xddcore/PineconePiWatch/Report&requirement/dev_img/%N)9%Y6C()[AU40SE[%3J6S.png

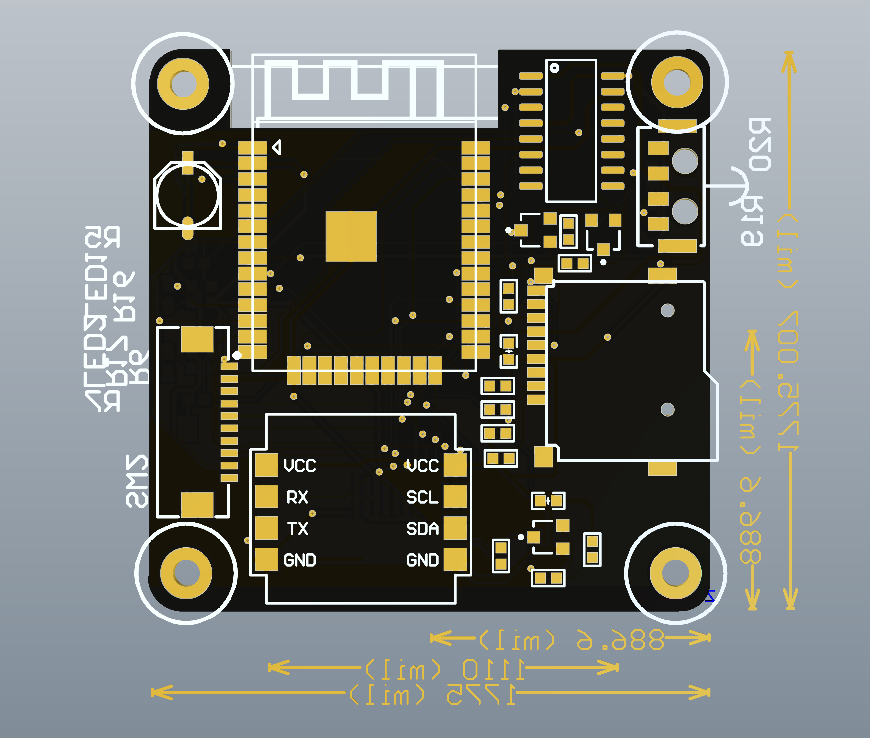
Report&requirement/dev_img/%N)9%Y6C()[AU40SE[%3J6S.png
