xddcore/PineconePiWatch/Report&requirement/dev_img/Django启动.png

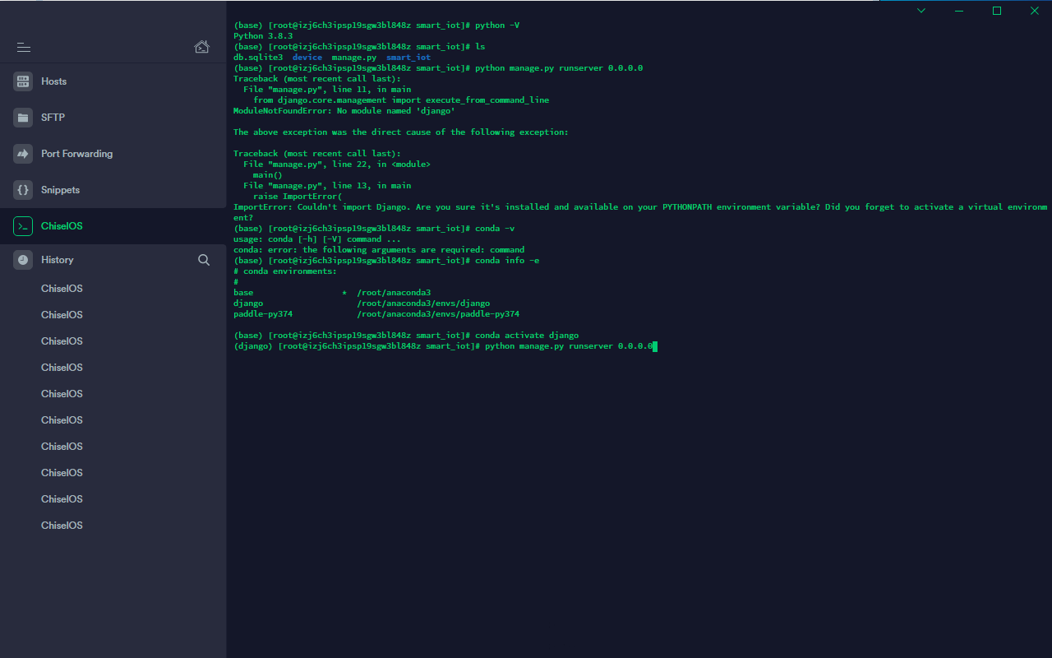
Report&requirement/dev_img/Django启动.png
