xddcore/PineconePiWatch/Report&requirement/dev_img/DRC无错误.png

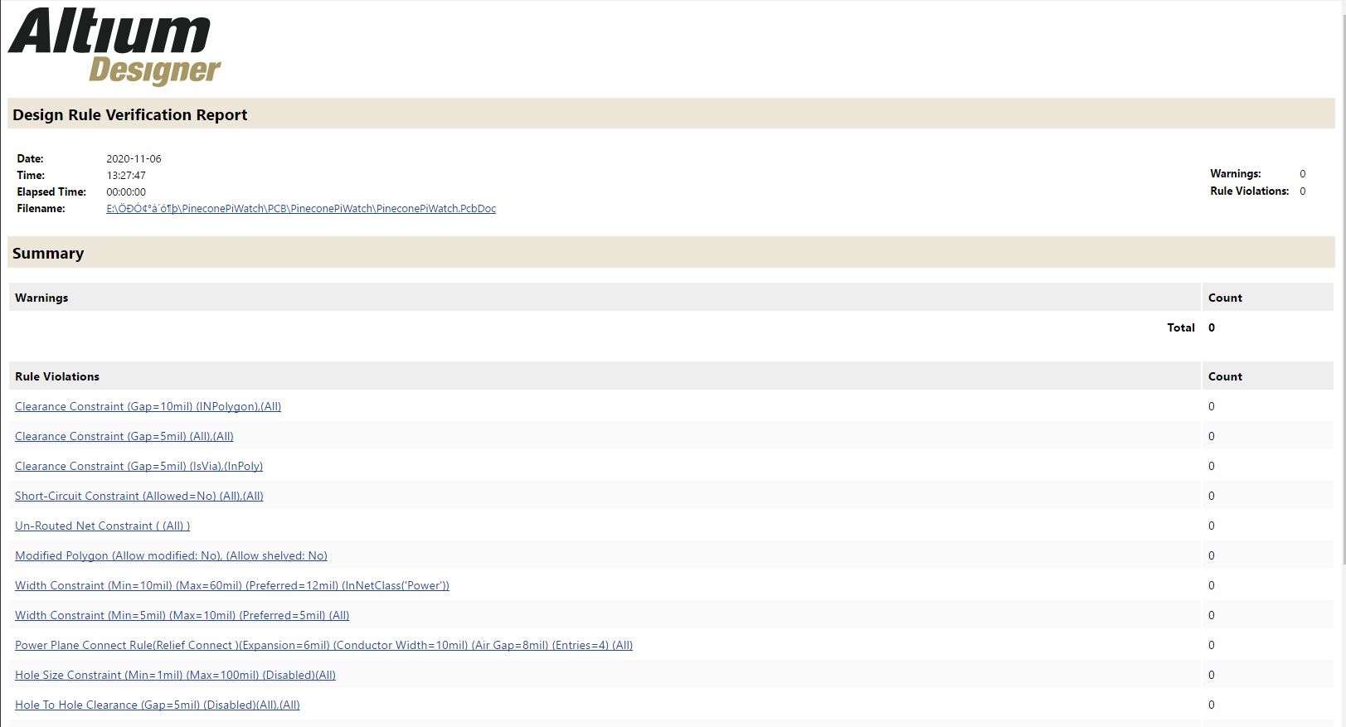
Report&requirement/dev_img/DRC无错误.png
