xddcore/PineconePiWatch/Report&requirement/dev_img/low power control/d21b8d4ec1d9de5b9760d6d338e170ff.png

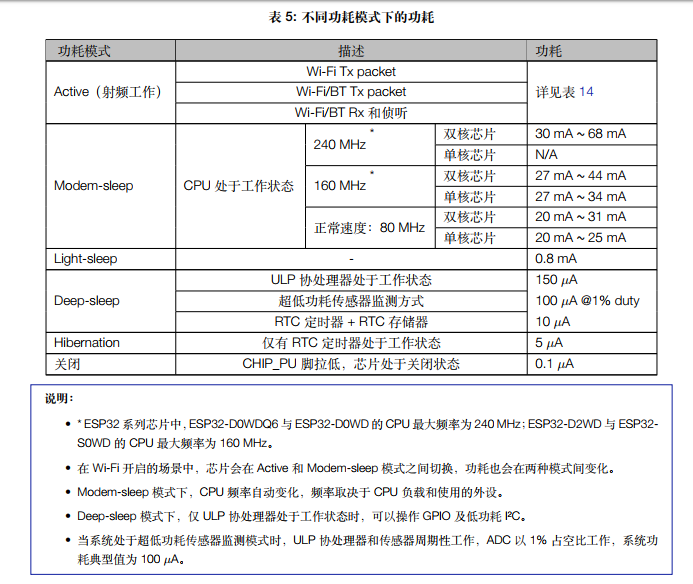
Report&requirement/dev_img/low power control/d21b8d4ec1d9de5b9760d6d338e170ff.png
