xddcore/PineconePiWatch/Report&requirement/dev_img/low power control/tft1.png

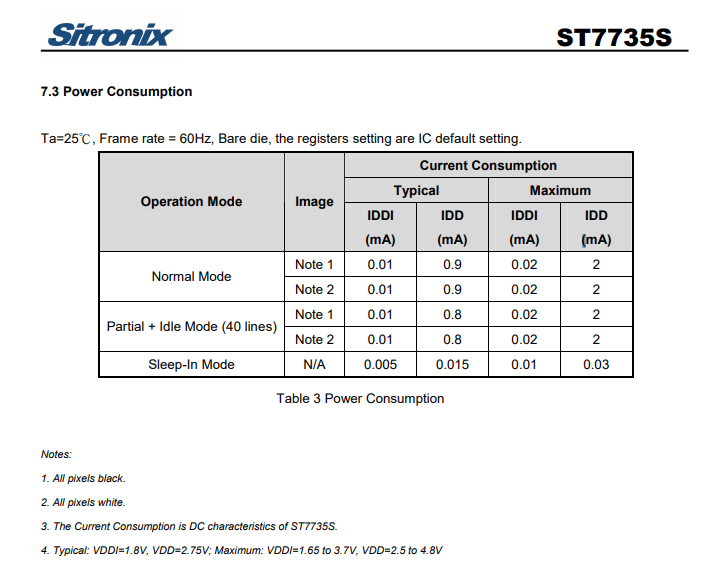
Report&requirement/dev_img/low power control/tft1.png
