xddcore/PineconePiWatch/Report&requirement/dev_img/low power control/v2-43d121ade4e81a2ae13ff51131ecac9f_720w.jpg

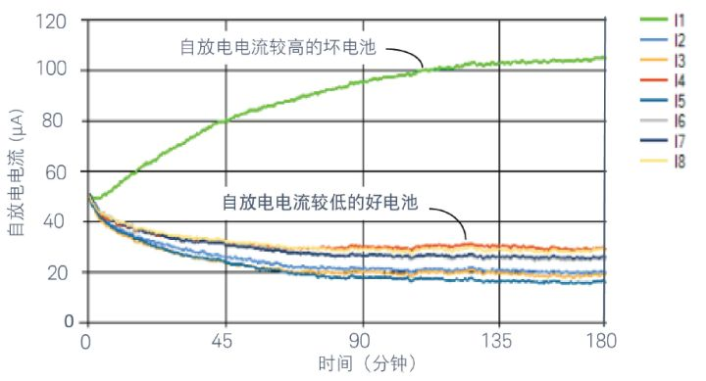
Report&requirement/dev_img/low power control/v2-43d121ade4e81a2ae13ff51131ecac9f_720w.jpg
