xddcore/PineconePiWatch/Report&requirement/dev_img/MQTT-2.png

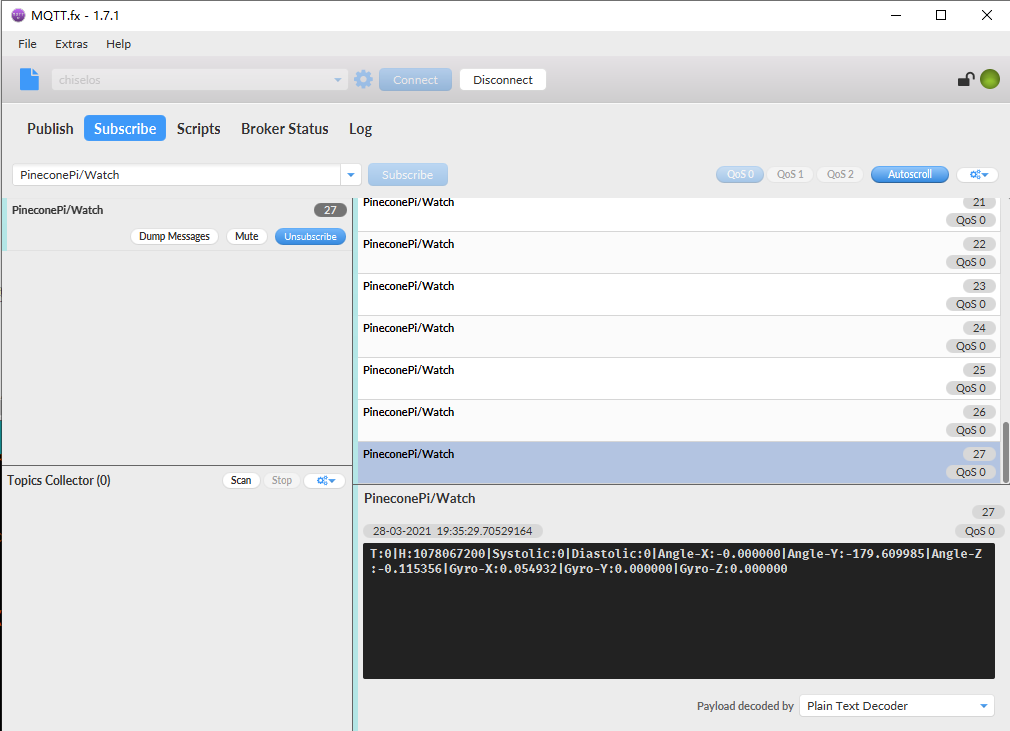
Report&requirement/dev_img/MQTT-2.png
