xddcore/PineconePiWatch/Report&requirement/dev_img/mqtt测试2.png

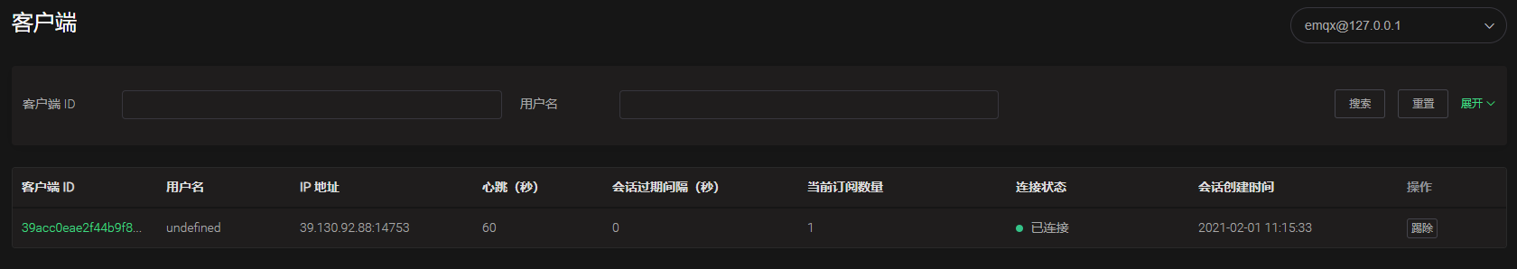
Report&requirement/dev_img/mqtt测试2.png
