xddcore/PineconePiWatch/Report&requirement/dev_img/mqtt测试.png

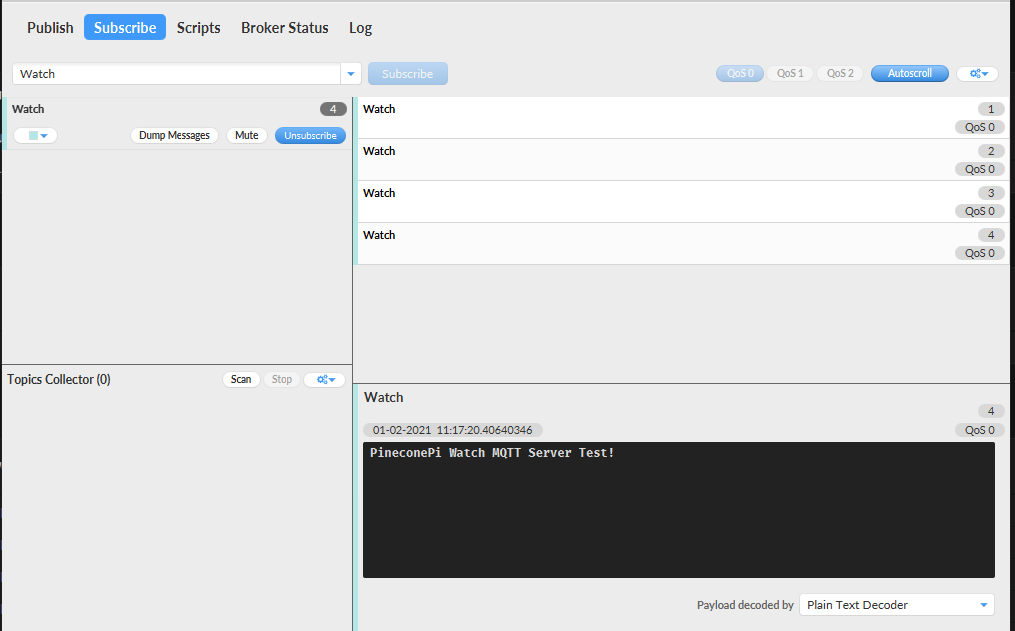
Report&requirement/dev_img/mqtt测试.png
