xddcore/PineconePiWatch/Report&requirement/dev_img/{$VM_AUJAC7O}LSEJL2]M8W.png

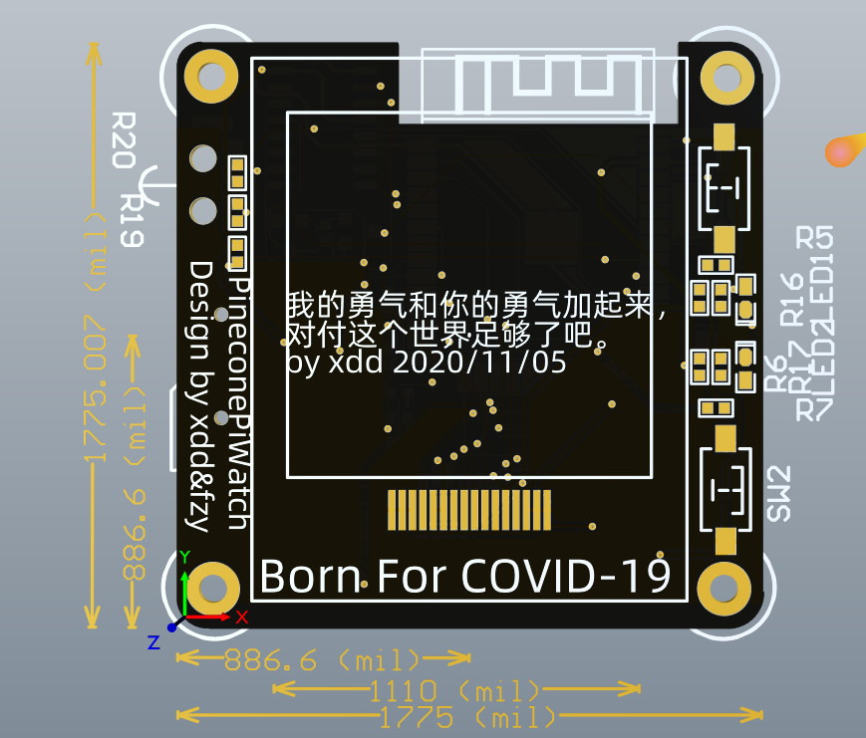
Report&requirement/dev_img/{$VM_AUJAC7O}LSEJL2]M8W.png
