xddcore/PineconePiWatch/Report&requirement/img/BOTTOM-PCB-1.png

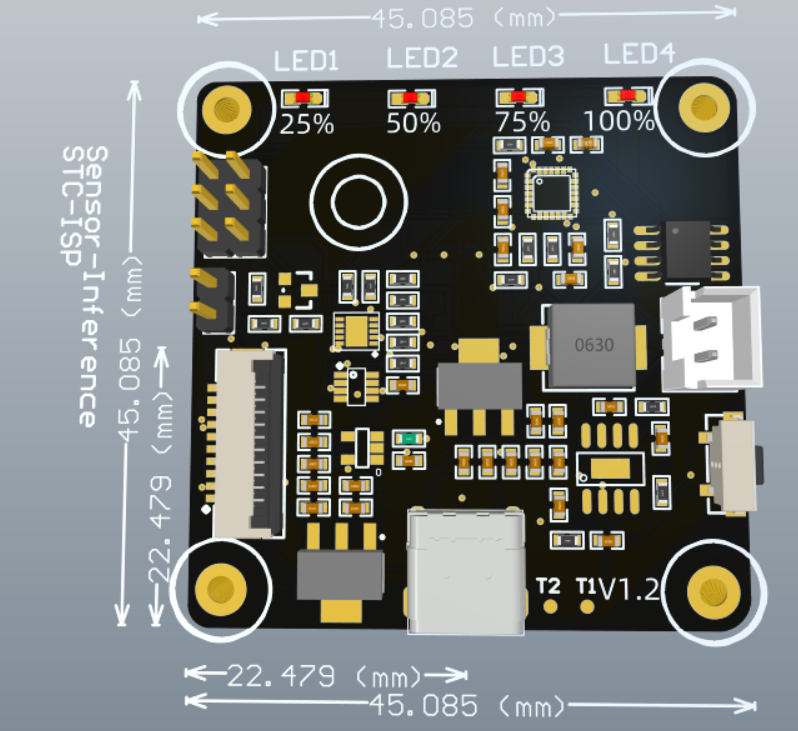
Report&requirement/img/BOTTOM-PCB-1.png
