xddcore/PineconePiWatch/Report&requirement/img/BUTTOM_PCB-2.png

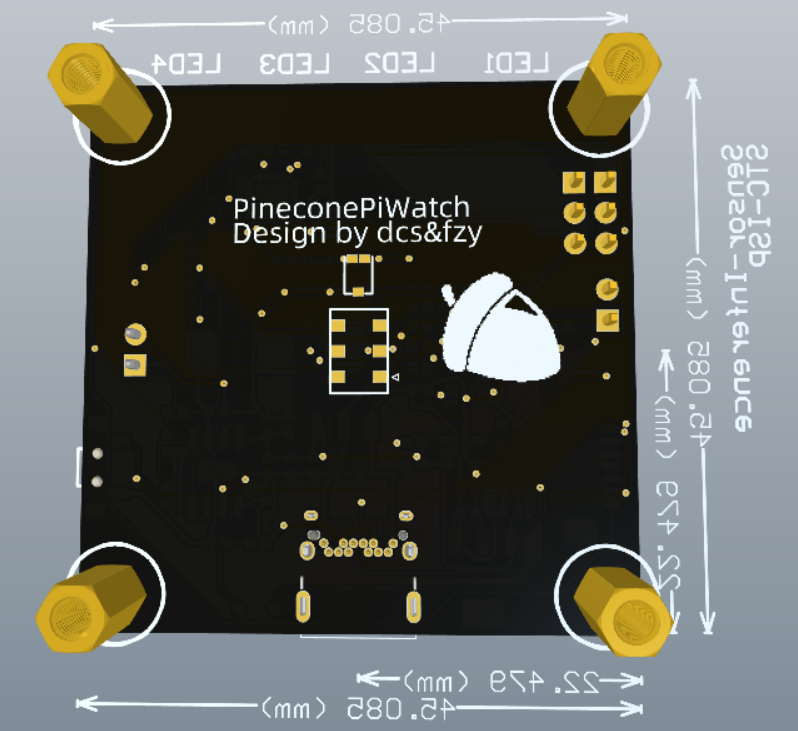
Report&requirement/img/BUTTOM_PCB-2.png
