xddcore/PineconePiWatch/Report&requirement/img/co-stc-code.png

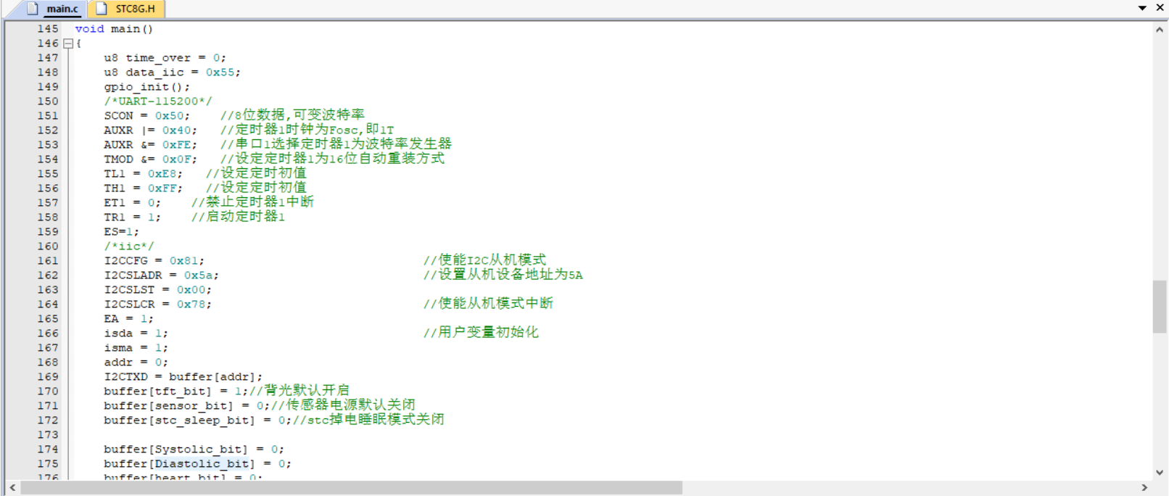
Report&requirement/img/co-stc-code.png
