xddcore/PineconePiWatch/Report&requirement/img/PCB3d仿真图.png

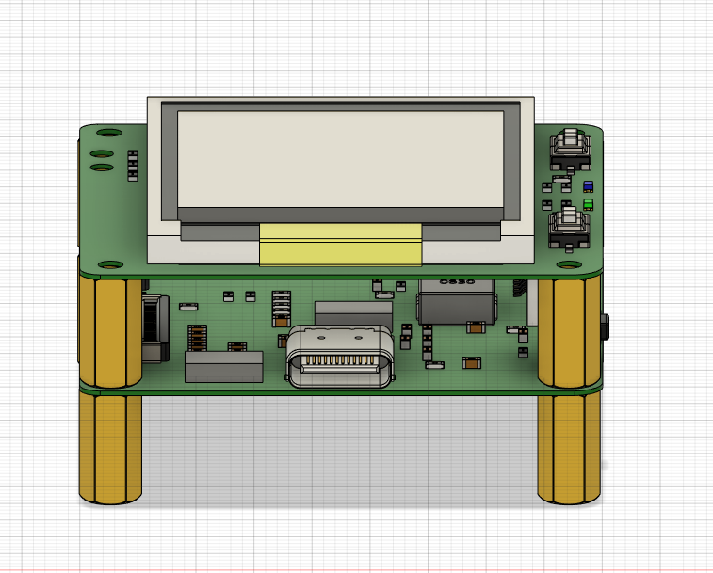
Report&requirement/img/PCB3d仿真图.png
