xddcore/PineconePiWatch/Report&requirement/img/TOP-PCB-1.png

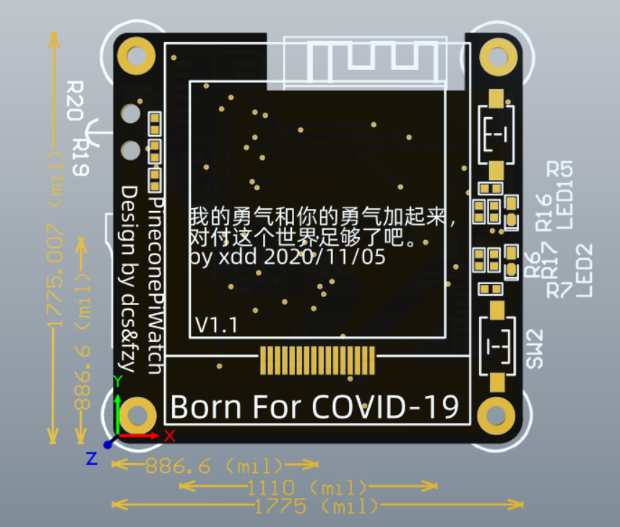
Report&requirement/img/TOP-PCB-1.png
