xddcore/PineconePiWatch/Report&requirement/img/TOP-PCB.png

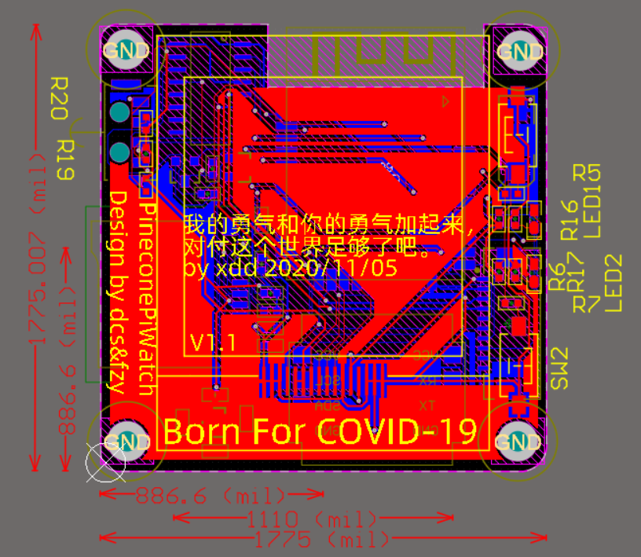
Report&requirement/img/TOP-PCB.png
