xddcore/PineconePiWatch/Report&requirement/img/web.png

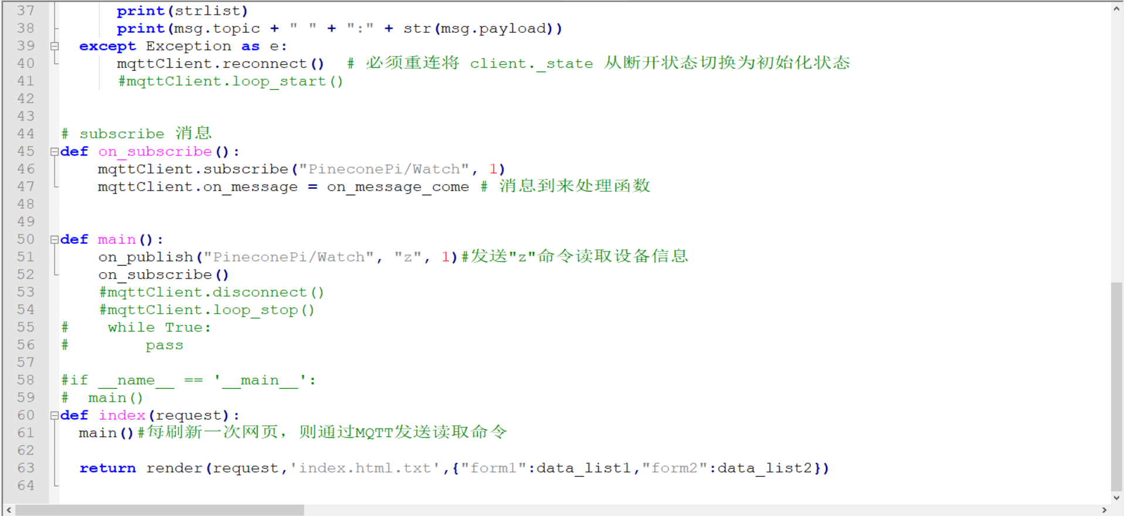
Report&requirement/img/web.png
