xddcore/PineconePiWatch/Report&requirement/img/单纯外壳3d仿真图.png

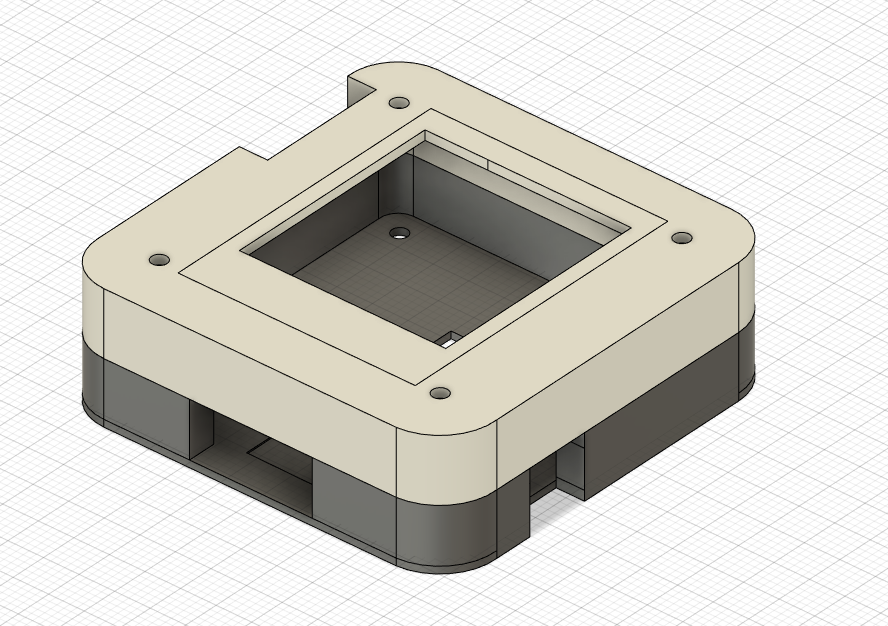
Report&requirement/img/单纯外壳3d仿真图.png
