xddcore/PineconePiWatch/Report&requirement/img/实物测试/IMG_0146.JPG

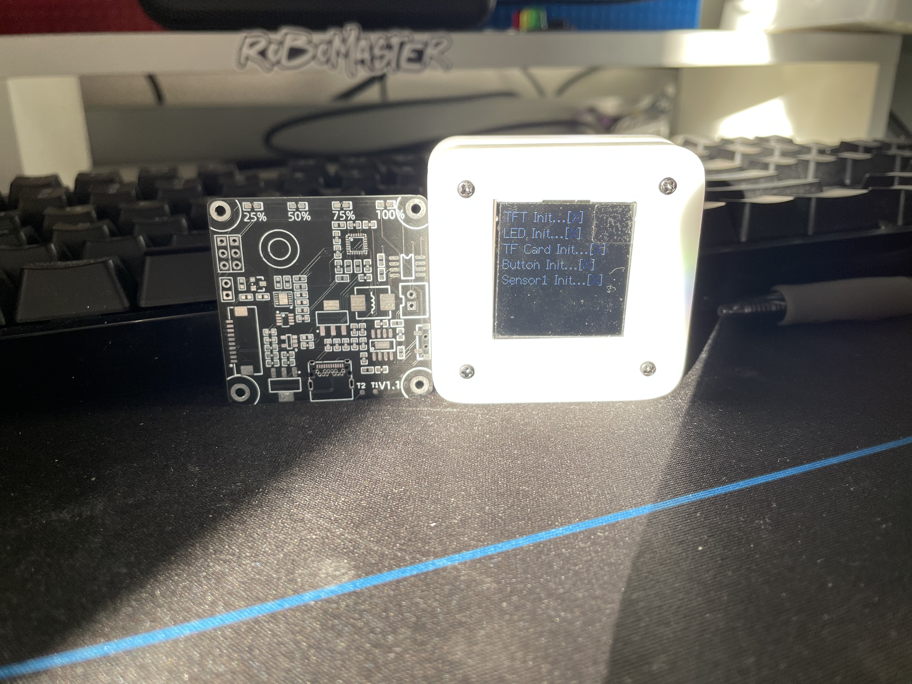
Report&requirement/img/实物测试/IMG_0146.JPG
