xddcore/PineconePiWatch/Report&requirement/img/实物测试/IMG_0759.JPG

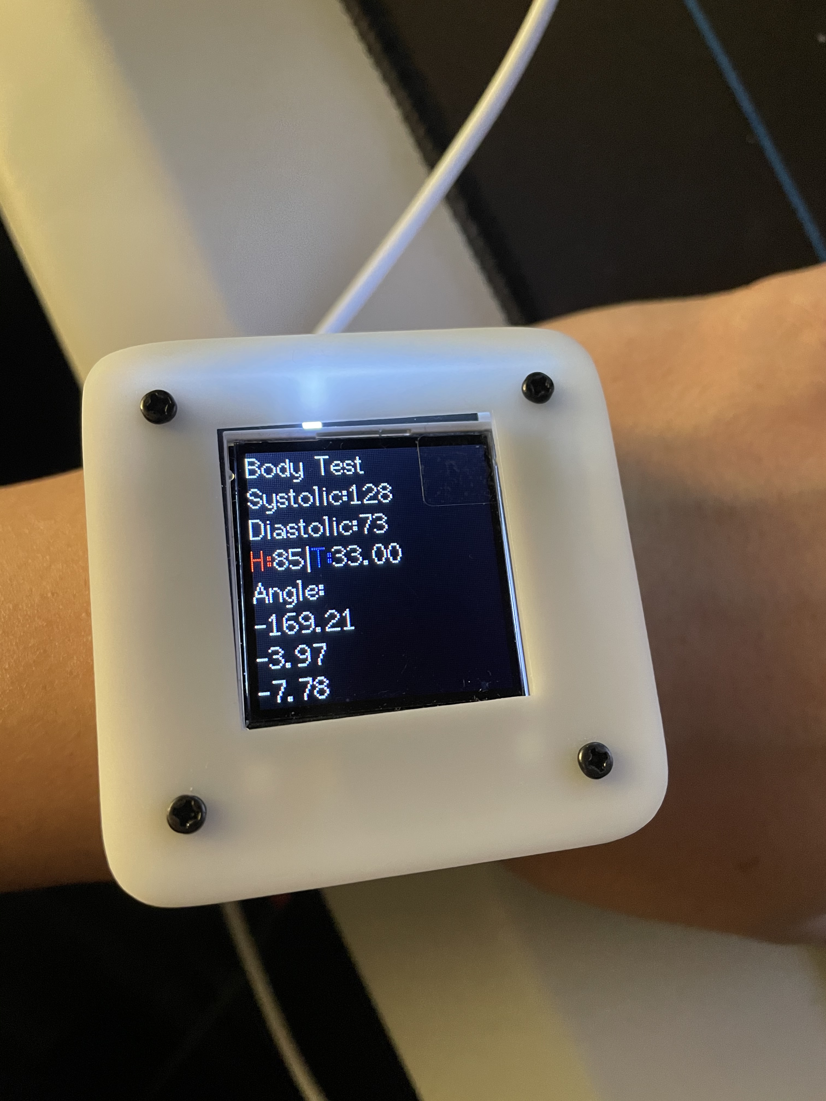
Report&requirement/img/实物测试/IMG_0759.JPG
