xddcore/PineconePiWatch/Report&requirement/img/实物测试/IMG_3872.JPG

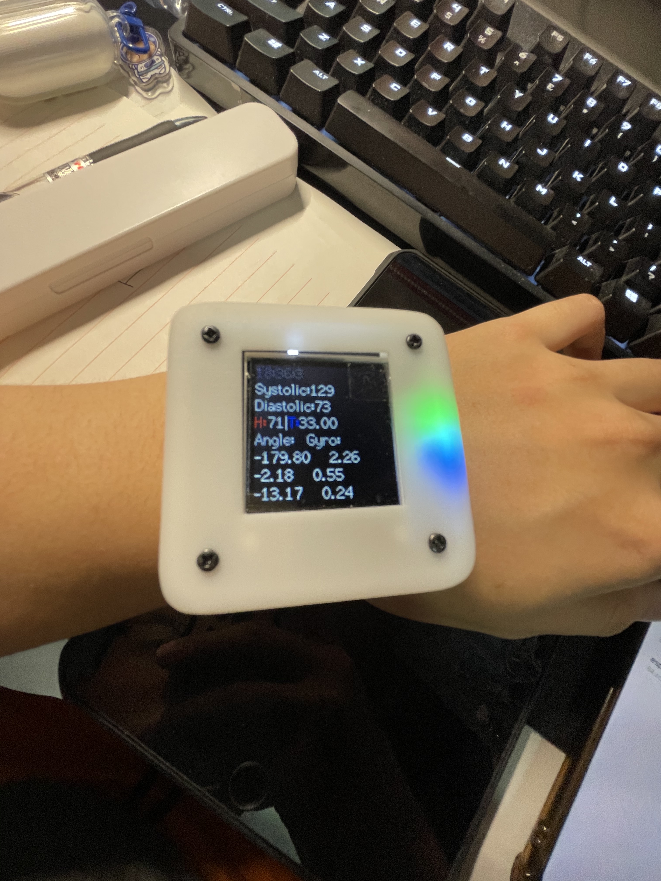
Report&requirement/img/实物测试/IMG_3872.JPG
