xddcore/PineconePiWatch/Report&requirement/img/实物测试/IMG_3876(20210328-190102).JPG

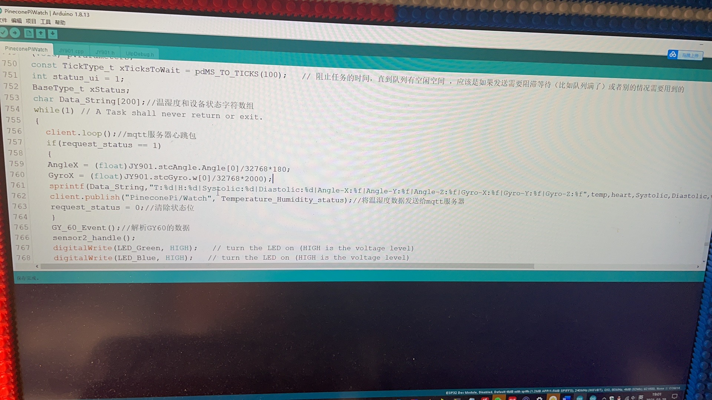
Report&requirement/img/实物测试/IMG_3876(20210328-190102).JPG
