xddcore/PineconePiWatch/Report&requirement/img/实物测试/IMG_3877.JPG

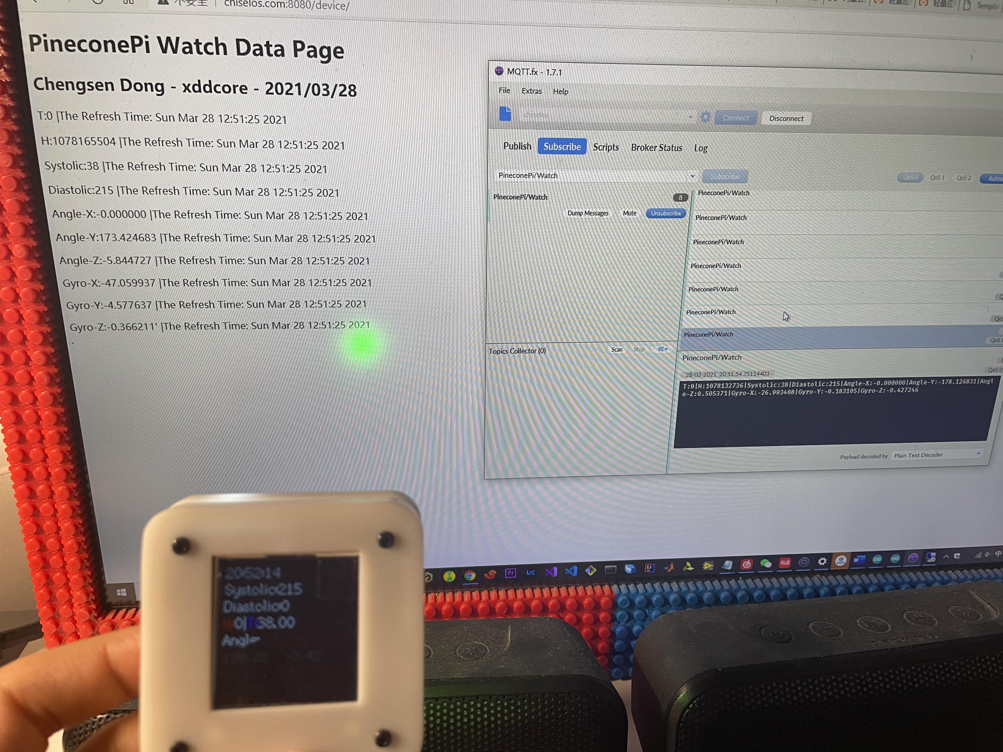
Report&requirement/img/实物测试/IMG_3877.JPG
