xddcore/PineconePiWatch/Report&requirement/img/实物测试/IMG_3879.PNG

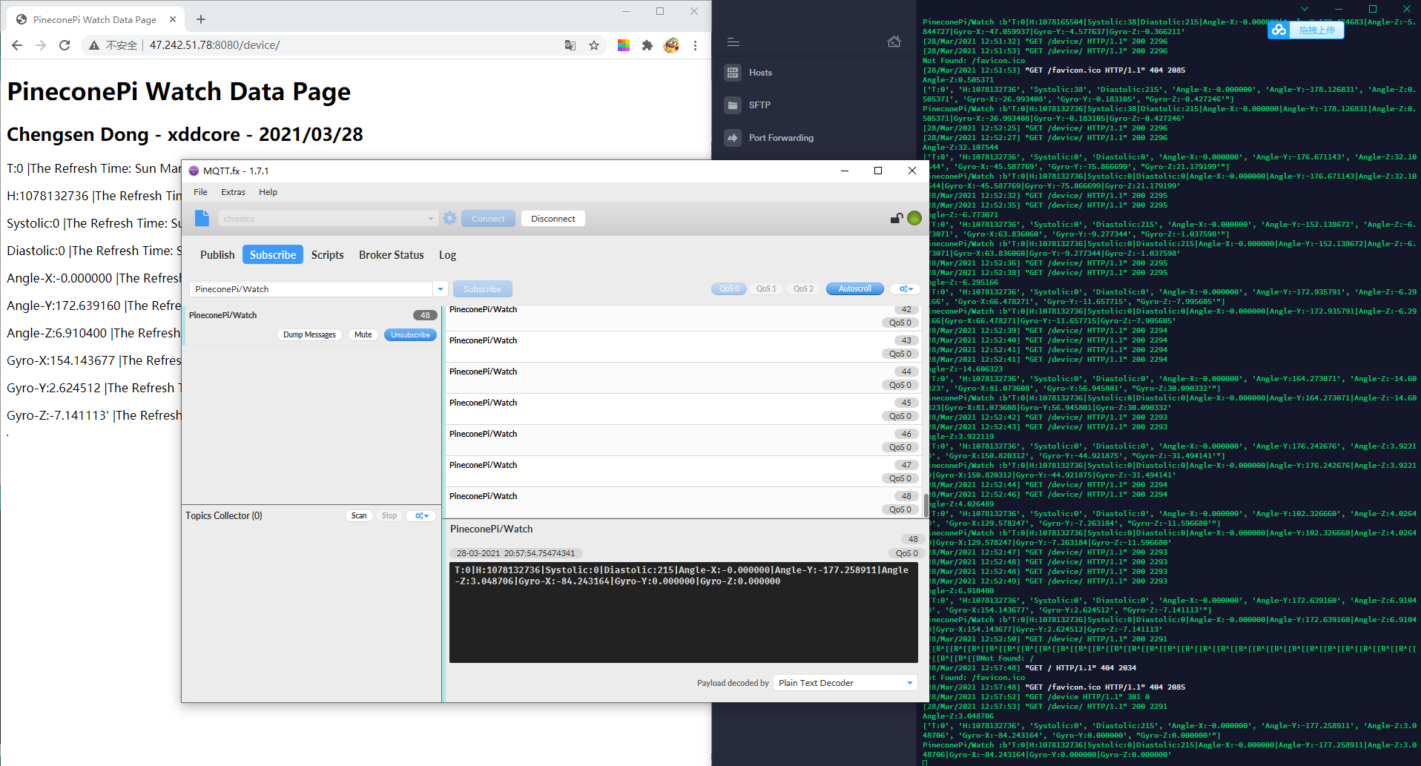
Report&requirement/img/实物测试/IMG_3879.PNG
