xddcore/PineconePiWatch/Report&requirement/img/带外壳3d仿真图2.png

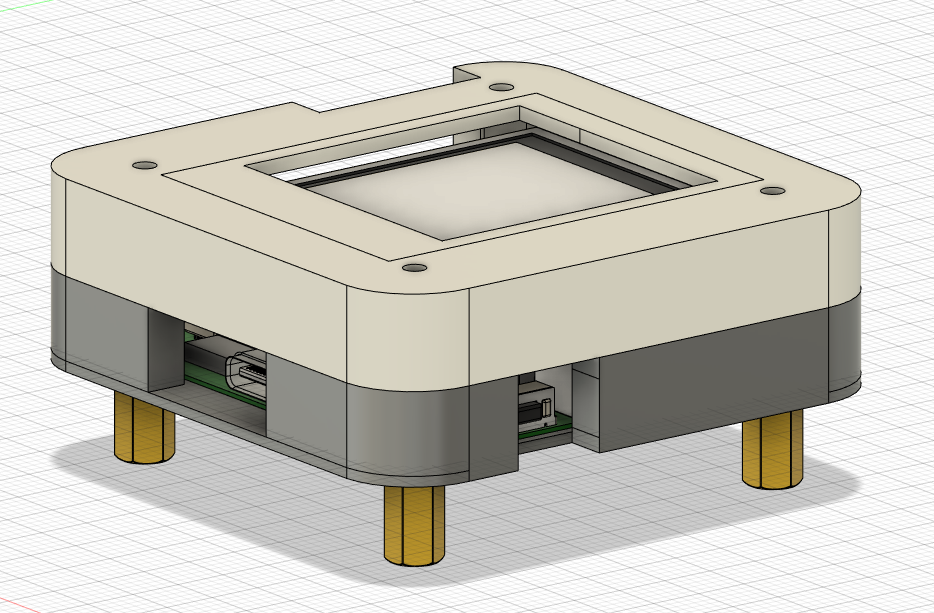
Report&requirement/img/带外壳3d仿真图2.png
