xddcore/PineconePiWatch/Report&requirement/img/底部PCB图片.png

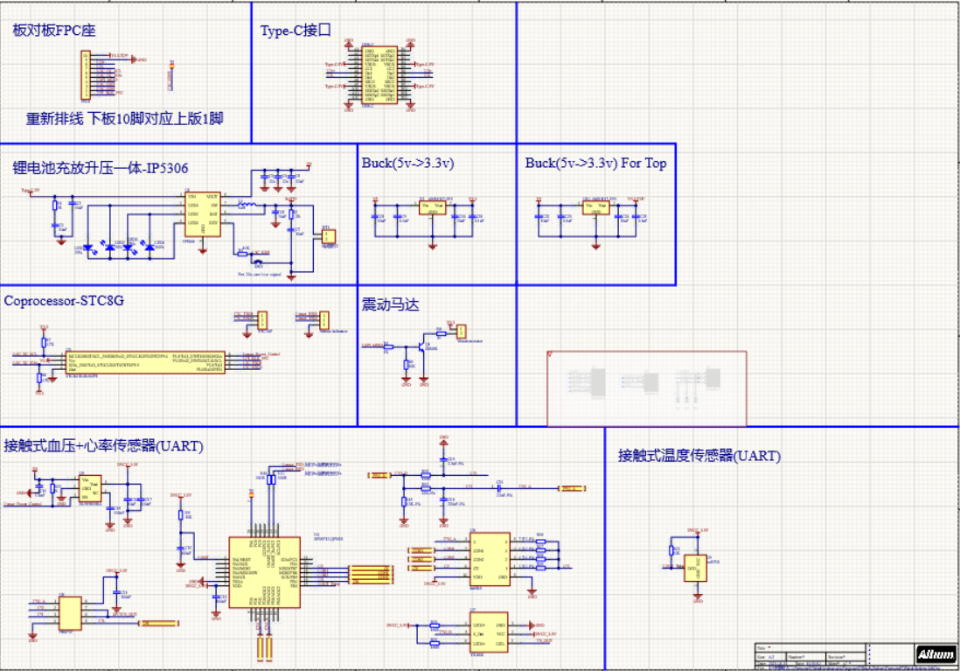
Report&requirement/img/底部PCB图片.png
