xddcore/PineconePiWatch/Report&requirement/img/甘特图2.png

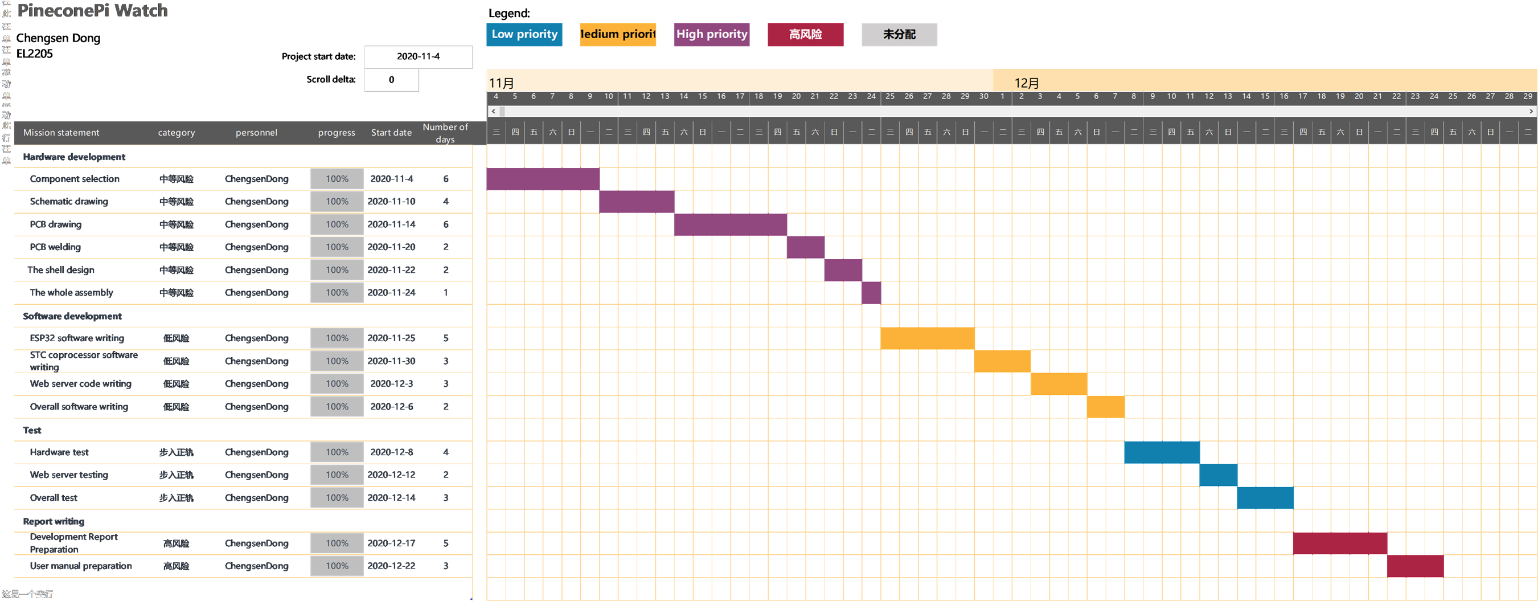
Report&requirement/img/甘特图2.png
