xddcore/PineconePiWatch/Report&requirement/img/顶部PCB图片.png

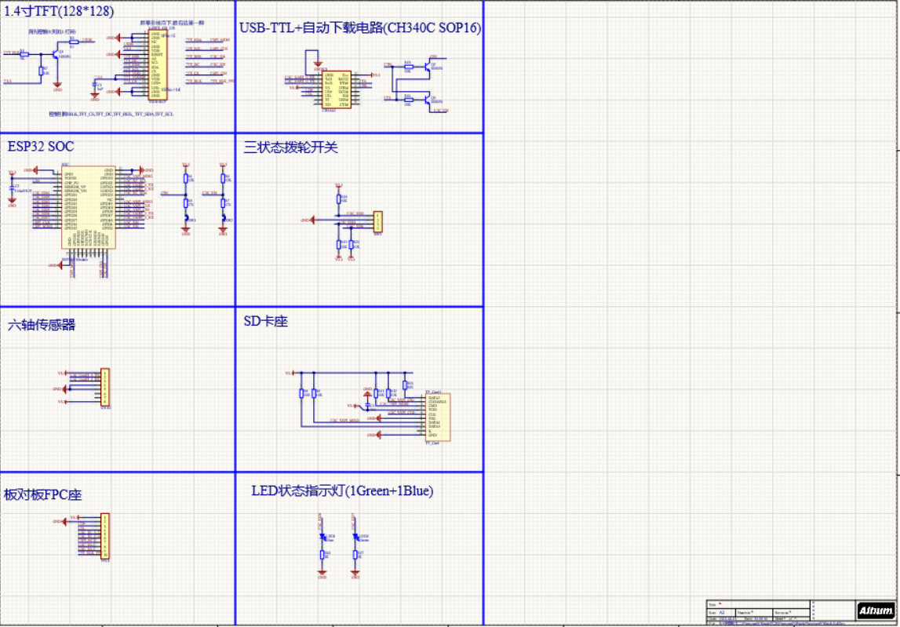
Report&requirement/img/顶部PCB图片.png
