xddcore/PineconePiWatch/CODE/ESP32-MAINPROCESSOR/PineconePiWatch/UlpDebug.h

#ifndef __ULPDEBUG_H__
#define __ULPDEBUG_H__

#include "esp32/ulp.h"

const char* ulpRegStr[] = {
  "R0",
  "R1",
  "R2",
  "R3",
};

const char* ulpPeriphStr[] = {
  "RTC_CNTL",
  "RTC_IO",
  "SARADC",
};

const char* ulpSarStr[] = {
  "RTC_CNTL",
  "RTC_IO",
  "SARADC",
};

const char* ulpSignStr[] = {
  "+",
  "-",
};

const char* ulpCmpStr[] = {
  "LT",
  "GE",
};

const char* ulpCmp2Str[] = {
  "R0 < ",
  "R0 >= ",
};

void ulpDisassemblerDump(int pos) {
  ulp_insn_t *prog = (ulp_insn_t*)&RTC_SLOW_MEM[pos];

  if(prog->halt.opcode==0 && RTC_SLOW_MEM[pos] !=0){
    Serial.printf("%04X : %08X DATA %5d\t\t\t\t// ST ADDR:0x%04X\n", pos, RTC_SLOW_MEM[pos], (int16_t)(RTC_SLOW_MEM[pos] & 0xFFFF), RTC_SLOW_MEM[pos] >> 21);
    return;
  }

  Serial.printf("%04X : %08X PROG ", pos, RTC_SLOW_MEM[pos]);

  switch( prog->halt.opcode ){
    case 0:               // NOP
                          Serial.printf("NOP\t\t\t\t// NOP");
                          break;

    case OPCODE_WR_REG:   // REG_WR
                          Serial.printf("REG_WR 0x%04X, %3d, %3d, %3d\t// %s[%d:%d] = %d", prog->wr_reg.addr, prog->wr_reg.high, prog->wr_reg.low, prog->wr_reg.data, ulpPeriphStr[prog->wr_reg.periph_sel], prog->wr_reg.high, prog->wr_reg.low, prog->wr_reg.data );
                          break;

    case OPCODE_RD_REG:   // REG_RD
                          Serial.printf("REG_RD 0x%04X, %3d, %3d\t// R0 = %s[%d:%d]", prog->rd_reg.addr, prog->rd_reg.high, prog->rd_reg.low, ulpPeriphStr[prog->rd_reg.periph_sel], prog->rd_reg.high, prog->rd_reg.low );
                          break;
    
    case OPCODE_I2C:      // I2C
                          if( prog->i2c.rw == 0 ){
                            Serial.printf("I2C_RD 0x%02X, %3d, %3d, 0x%02X", prog->i2c.i2c_addr, prog->i2c.high_bits, prog->i2c.low_bits, prog->i2c.i2c_sel);
                          } else {
                            Serial.printf("I2C_WR 0x%02X, 0x%02X, %3d, %3d, 0x%02X", prog->i2c.i2c_addr, prog->i2c.data, prog->i2c.high_bits, prog->i2c.low_bits, prog->i2c.i2c_sel);
                          }
                          break;
    
    case OPCODE_DELAY:    // WAIT
                          Serial.printf("WAIT   %3d\t\t\t// Delay %d", prog->delay.cycles, prog->delay.cycles );
                          break;
    
    case OPCODE_ADC:      // ADC
                          Serial.printf("ADC    %s, %s, %3d, %d", ulpPeriphStr[prog->adc.dreg], ulpSarStr[prog->adc.sar_sel], prog->adc.mux, prog->adc.cycles );
                          break;
    
    case OPCODE_ST:       // ST
                          Serial.printf("ST     %s, %s, %3d\t\t\t// MEM[%s+%d] = %s", ulpRegStr[prog->st.dreg], ulpRegStr[prog->st.sreg], prog->st.offset, ulpRegStr[prog->st.sreg], prog->st.offset, ulpRegStr[prog->st.dreg] );
                          break;
    
    case OPCODE_ALU:      // ALU
                          if(prog->alu_reg.sel == ALU_SEL_ADD){
                            // ADD
                            if(prog->alu_reg.sub_opcode == SUB_OPCODE_ALU_REG){
                              // reg
                              Serial.printf("ADD    %s, %s, %s\t\t\t// %s = %s + %s", ulpRegStr[prog->alu_reg.dreg], ulpRegStr[prog->alu_reg.sreg], ulpRegStr[prog->alu_reg.treg], ulpRegStr[prog->alu_reg.dreg], ulpRegStr[prog->alu_reg.sreg], ulpRegStr[prog->alu_reg.treg]);
                            } else {
                              // imm
                              Serial.printf("ADD    %s, %s, %3d\t\t\t// %s = %s + %d", ulpRegStr[prog->alu_imm.dreg], ulpRegStr[prog->alu_imm.sreg], (int16_t)prog->alu_imm.imm, ulpRegStr[prog->alu_imm.dreg], ulpRegStr[prog->alu_imm.sreg], (int16_t)prog->alu_imm.imm);
                            }
                          } else if(prog->alu_reg.sel == ALU_SEL_SUB){
                            // SUB
                            if(prog->alu_reg.sub_opcode == SUB_OPCODE_ALU_REG){
                              // reg
                              Serial.printf("SUB    %s, %s, %s\t\t\t// %s = %s - %s", ulpRegStr[prog->alu_reg.dreg], ulpRegStr[prog->alu_reg.sreg], ulpRegStr[prog->alu_reg.treg], ulpRegStr[prog->alu_reg.dreg], ulpRegStr[prog->alu_reg.sreg], ulpRegStr[prog->alu_reg.treg]);
                            } else {
                              // imm
                              Serial.printf("SUB    %s, %s, %3d\t\t\t// %s = %s - %d", ulpRegStr[prog->alu_imm.dreg], ulpRegStr[prog->alu_imm.sreg], (int16_t)prog->alu_imm.imm, ulpRegStr[prog->alu_imm.dreg], ulpRegStr[prog->alu_imm.sreg], (int16_t)prog->alu_imm.imm);
                            }
                          } else if(prog->alu_reg.sel == ALU_SEL_AND){
                            // AND
                            if(prog->alu_reg.sub_opcode == SUB_OPCODE_ALU_REG){
                              // reg
                              Serial.printf("AND    %s, %s, %s\t\t\t// %s = %s & %s", ulpRegStr[prog->alu_reg.dreg], ulpRegStr[prog->alu_reg.sreg], ulpRegStr[prog->alu_reg.treg], ulpRegStr[prog->alu_reg.dreg], ulpRegStr[prog->alu_reg.sreg], ulpRegStr[prog->alu_reg.treg]);
                            } else {
                              // imm
                              Serial.printf("AND    %s, %s, %3d\t\t\t// %s = %s & %d", ulpRegStr[prog->alu_imm.dreg], ulpRegStr[prog->alu_imm.sreg], (int16_t)prog->alu_imm.imm, ulpRegStr[prog->alu_imm.dreg], ulpRegStr[prog->alu_imm.sreg], (int16_t)prog->alu_imm.imm);
                            }
                          } else if(prog->alu_reg.sel == ALU_SEL_OR){
                            // OR
                            if(prog->alu_reg.sub_opcode == SUB_OPCODE_ALU_REG){
                              // reg
                              Serial.printf("OR     %s, %s, %s\t\t\t// %s = %s | %s", ulpRegStr[prog->alu_reg.dreg], ulpRegStr[prog->alu_reg.sreg], ulpRegStr[prog->alu_reg.treg], ulpRegStr[prog->alu_reg.dreg], ulpRegStr[prog->alu_reg.sreg], ulpRegStr[prog->alu_reg.treg]);
                            } else {
                              // imm
                              Serial.printf("OR     %s, %s, %3d\t\t\t// %s = %s | %d", ulpRegStr[prog->alu_imm.dreg], ulpRegStr[prog->alu_imm.sreg], (int16_t)prog->alu_imm.imm, ulpRegStr[prog->alu_imm.dreg], ulpRegStr[prog->alu_imm.sreg], (int16_t)prog->alu_imm.imm);
                            }
                          } else if(prog->alu_reg.sel == ALU_SEL_LSH){
                            // LSH
                            if(prog->alu_reg.sub_opcode == SUB_OPCODE_ALU_REG){
                              // reg
                              Serial.printf("LSH    %s, %s, %s\t\t\t// %s = %s << %s", ulpRegStr[prog->alu_reg.dreg], ulpRegStr[prog->alu_reg.sreg], ulpRegStr[prog->alu_reg.treg], ulpRegStr[prog->alu_reg.dreg], ulpRegStr[prog->alu_reg.sreg], ulpRegStr[prog->alu_reg.treg]);
                            } else {
                              // imm
                              Serial.printf("LSH    %s, %s, %3d\t\t\t// %s = %s << %d", ulpRegStr[prog->alu_imm.dreg], ulpRegStr[prog->alu_imm.sreg], (int16_t)prog->alu_imm.imm, ulpRegStr[prog->alu_imm.dreg], ulpRegStr[prog->alu_imm.sreg], (int16_t)prog->alu_imm.imm);
                            }
                          } else if(prog->alu_reg.sel == ALU_SEL_RSH){
                            // RSH
                            if(prog->alu_reg.sub_opcode == SUB_OPCODE_ALU_REG){
                              // reg
                              Serial.printf("RSH    %s, %s, %s\t\t\t// %s = %s >> %s", ulpRegStr[prog->alu_reg.dreg], ulpRegStr[prog->alu_reg.sreg], ulpRegStr[prog->alu_reg.treg], ulpRegStr[prog->alu_reg.dreg], ulpRegStr[prog->alu_reg.sreg], ulpRegStr[prog->alu_reg.treg]);
                            } else {
                              // imm
                              Serial.printf("RSH    %s, %s, %3d\t\t\t// %s = %s >> %d", ulpRegStr[prog->alu_imm.dreg], ulpRegStr[prog->alu_imm.sreg], (int16_t)prog->alu_imm.imm, ulpRegStr[prog->alu_imm.dreg], ulpRegStr[prog->alu_imm.sreg], (int16_t)prog->alu_imm.imm);
                            }
                          } else if(prog->alu_reg.sel == ALU_SEL_MOV){
                            // MOVE
                            if(prog->alu_reg.sub_opcode == SUB_OPCODE_ALU_REG){
                              // reg
                              Serial.printf("MOVE   %s, %s\t\t\t// %s = %s", ulpRegStr[prog->alu_reg.dreg], ulpRegStr[prog->alu_reg.sreg], ulpRegStr[prog->alu_reg.dreg], ulpRegStr[prog->alu_reg.sreg]);
                            } else {
                              // imm
                              Serial.printf("MOVE   %s, %3d\t\t\t// %s = %d", ulpRegStr[prog->alu_imm.dreg], (int16_t)prog->alu_imm.imm, ulpRegStr[prog->alu_imm.dreg], (int16_t)prog->alu_imm.imm);
                            }
                          }
                          break;
    
    case OPCODE_BRANCH:   // JUML
                          if(prog->b.sub_opcode == SUB_OPCODE_B){
                            // SUB_OPCODE_B(JUMP)
                            Serial.printf("JUMPR  %s%3d, %3d, %s\t\t// IF %s%d THAN GOTO 0x%04X", ulpSignStr[prog->b.sign], prog->b.offset, prog->b.imm, ulpCmpStr[prog->b.cmp], ulpCmp2Str[prog->b.cmp], prog->b.imm, prog->b.sign == 0 ? pos + prog->b.offset : pos - prog->b.offset);
                          } else {
                            // SUB_OPCODE_BX(DIRECT JUMP)
                            if( prog->bx.type == BX_JUMP_TYPE_DIRECT ){
                              // BX_JUMP_TYPE_DIRECT
                              if( prog->bx.reg == 1 ){
                                // reg
                                Serial.printf("JUMP   %s\t\t\t// GOTO %s", ulpRegStr[prog->bx.dreg], ulpRegStr[prog->bx.dreg]);
                              } else {
                                // imm
                                Serial.printf("JUMP   0x%04X\t\t\t// GOTO 0x%04X", prog->bx.addr, prog->bx.addr);
                              }                              
                            } else if( prog->bx.type == BX_JUMP_TYPE_ZERO ) {
                              // EQ
                              if( prog->bx.reg == 1 ){
                                // reg
                                Serial.printf("JUMP   %s, EQ", ulpRegStr[prog->bx.dreg]);
                              } else {
                                // imm
                                Serial.printf("JUMP   0x%04X, EQ", prog->bx.addr);
                              }                              
                            } else if( prog->bx.type == BX_JUMP_TYPE_OVF ){
                              // OV
                              if( prog->bx.reg == 1 ){
                                // reg
                                Serial.printf("JUMP   %s, OV", ulpRegStr[prog->bx.dreg]);
                              } else {
                                // imm
                                Serial.printf("JUMP   0x%04X, OV", prog->bx.addr);
                              }                              
                            }
                          }
                          break;
    
    case OPCODE_END:      // WAKE
                          Serial.printf("WAKE\t\t\t\t// WAKE");
                          break;
    
    case OPCODE_TSENS:    // TSENS
                          Serial.printf("TSENS  %s, %3d", ulpRegStr[prog->tsens.dreg], prog->tsens.wait_delay);
                          break;
    
    case OPCODE_HALT:     // HALT
                          Serial.printf("HALT\t\t\t\t// HALT");
                          break;
    
    case OPCODE_LD:       // LD
                          Serial.printf("LD     %s, %s, %3d\t\t\t// %s = MEM[%s+%d]", ulpRegStr[prog->ld.dreg], ulpRegStr[prog->ld.sreg], prog->ld.offset, ulpRegStr[prog->ld.dreg], ulpRegStr[prog->ld.sreg], prog->ld.offset);
                          break;
    
    case OPCODE_MACRO:    // MACRO
                          Serial.printf("MACRO");
                          break;

    default:              // Unknown
                          Serial.printf("Unknown");
                          break;
  }
  Serial.printf("\n");
}

void ulpDump(int start = 0, int end = 2047, int programAddr = 0) {
  Serial.printf("====================================\n");
  for ( int i = start ; i < end ; i++ ) {
    ulpDisassemblerDump(i);

    if( i < (2047-5) && RTC_SLOW_MEM[i+1] == 0 && RTC_SLOW_MEM[i+2] == 0 && RTC_SLOW_MEM[i+3] == 0 && RTC_SLOW_MEM[i+4] == 0 ){
      break;
    }
  }
}

#endif // __ULPDEBUG_H__
